dmitrymironov/usbpark/audi/images/bs.png

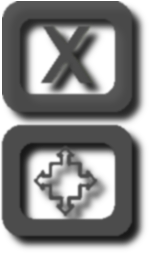
audi/images/bs.png
