dmitrymironov/usbpark/parktronic/images/PARKTRONIC_EMPTY.jpg

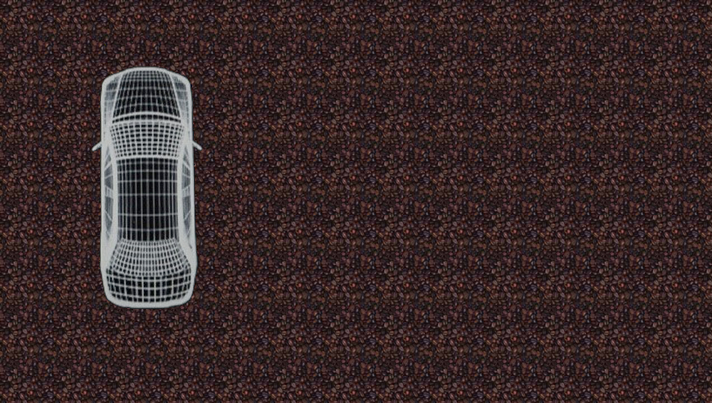
parktronic/images/PARKTRONIC_EMPTY.jpg
