dmitrymironov/usbpark/parktronic/images/PARKTRONIC_EMPTY_NO_VIDEO.jpg

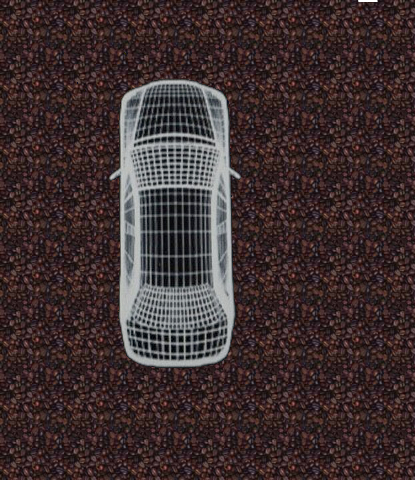
parktronic/images/PARKTRONIC_EMPTY_NO_VIDEO.jpg
