dmitrymironov/usbpark/parktronic/win32.cpp

/*
----------------------------------------------------------------------
CONTENTS of this file is private property of Novorado, LLC
======================================================================
Source Code is distributed for reference purposes only for Novorado 
customers. For other uses, please contact Novorado 
http://www.novorado.com or on our facebook/twitter page

You may use source code in your non-commercial and educational 
and customization projects free of charge.  

Novorado specializes in custom software and hardware design
and engineering services.
======================================================================
*/
#include	<list>
#include	<string>
#include	<deque>
#include	<iostream>

#ifndef _MSC_VER
#   include <wtypes.h>
#   include <unknwn.h>
#   include <ole2.h>
#   include <limits.h>
#   ifdef _WINGDI_
#      undef _WINGDI_
#   endif
#   define _WINGDI_ 1
#   define AM_NOVTABLE
#   define _OBJBASE_H_
#   undef _X86_
#   ifndef _I64_MAX
#     define _I64_MAX LONG_LONG_MAX
#   endif
#   define LONGLONG long long
#endif

#include	<dshow.h>

#include	"ParkSetup.h"

// Part of vlc_charset.h
#ifdef WIN32
//LIBVLC_USED
static inline char *FromWide (const wchar_t *wide)
{
    size_t len = WideCharToMultiByte (CP_UTF8, 0, wide, -1, NULL, 0, NULL, NULL);
    if (len == 0)
        return NULL;

    char *out = (char *)malloc (len);

    if (out)
        WideCharToMultiByte (CP_UTF8, 0, wide, -1, out, len, NULL, NULL);
    return out;
}
#endif

/* FindCaptureDevices:: This Function had two purposes :
    Returns the list of capture devices when p_listdevices != NULL
    Creates an IBaseFilter when p_devicename corresponds to an existing devname
   These actions *may* be requested whith a single call.
*/
#include	<ocidl.h>

static IBaseFilter *
FindCaptureDevice( std::string *p_devicename,
                   std::list<std::string> *p_listdevices, bool b_audio )
{
    IBaseFilter *p_base_filter = NULL;
    IMoniker *p_moniker = NULL;
    ULONG i_fetched;
    HRESULT hr;
    std::list<std::string> devicelist;

    /* Create the system device enumerator */
    ICreateDevEnum *p_dev_enum = NULL;

    hr = CoCreateInstance( CLSID_SystemDeviceEnum, NULL, CLSCTX_INPROC,
                           IID_ICreateDevEnum, (void **)&p_dev_enum );
    if( FAILED(hr) )
    {
        std::cerr << "failed to create the device enumerator (0x" << std::hex << hr << std::dec << ")" << std::endl;
        return NULL;
    }

    /* Create an enumerator for the video capture devices */
    IEnumMoniker *p_class_enum = NULL;
    if( !b_audio )
        hr = p_dev_enum->CreateClassEnumerator( CLSID_VideoInputDeviceCategory,
                                                &p_class_enum, 0 );
    else
        hr = p_dev_enum->CreateClassEnumerator( CLSID_AudioInputDeviceCategory,
                                                &p_class_enum, 0 );
    p_dev_enum->Release();
    if( FAILED(hr) )
    {
        std::cerr << "failed to create the class enumerator (0x" << std::hex << hr << std::dec << ")" << std::endl;
        return NULL;
    }

    /* If there are no enumerators for the requested type, then
     * CreateClassEnumerator will succeed, but p_class_enum will be NULL */
    if( p_class_enum == NULL )
    {
        std::cerr <<  "no " << ( b_audio ? "audio" : "video" ) << " capture device was detected" << std::endl;
        return NULL;
    }

    /* Enumerate the devices */

    /* Note that if the Next() call succeeds but there are no monikers,
     * it will return S_FALSE (which is not a failure). Therefore, we check
     * that the return code is S_OK instead of using SUCCEEDED() macro. */

    while( p_class_enum->Next( 1, &p_moniker, &i_fetched ) == S_OK )
    {
        /* Getting the property page to get the device name */
        IPropertyBag *p_bag;
        hr = p_moniker->BindToStorage( 0, 0, IID_IPropertyBag,
                                       (void **)&p_bag );
        if( SUCCEEDED(hr) )
        {
            VARIANT var;
            var.vt = VT_BSTR;
            hr = p_bag->Read( L"FriendlyName", &var, NULL );
            p_bag->Release();
            if( SUCCEEDED(hr) )
            {
                char *p_buf = FromWide( var.bstrVal );
                std::string devname = std::string(p_buf);
                free( p_buf) ;

                int dup = 0;
                /* find out if this name is already used by a previously found device */
                std::list<std::string>::const_iterator iter = devicelist.begin();
                std::list<std::string>::const_iterator end = devicelist.end();
                std::string ordevname = devname ;
                while ( iter != end )
                {
                    if( 0 == (*iter).compare( devname ) )
                    { /* devname is on the list. Try another name with sequence
                         number apended and then rescan until a unique entry is found*/
                         char seq[16];
                         snprintf(seq, 16, " #%d", ++dup);
                         devname = ordevname + seq;
                         iter = devicelist.begin();
                    }
                    else
                         ++iter;
                }
                devicelist.push_back( devname );

                if( p_devicename && *p_devicename == devname )
                {
                    std::cout << "asked for " << p_devicename->c_str() << ", binding to " << devname.c_str()  << std::endl;
                    /* NULL possibly means we don't need BindMoniker BindCtx ?? */
                    hr = p_moniker->BindToObject( NULL, 0, IID_IBaseFilter,
                                                  (void **)&p_base_filter );
                    if( FAILED(hr) )
                    {
                        std::cerr << "couldn't bind moniker to filter object (0x" << std::hex << hr << std::dec << ")" << std::endl;
                        p_moniker->Release();
                        p_class_enum->Release();
                        return NULL;
                    }
                    p_moniker->Release();
                    p_class_enum->Release();
                    return p_base_filter;
                }
            }
        }

        p_moniker->Release();
    }

    p_class_enum->Release();

    if( p_listdevices ) {
    devicelist.sort();
    *p_listdevices = devicelist;
    }
    return NULL;
}


std::list<std::string> Novorado::Parking::WebCamTab::getCaptureDevices()
{
	std::list<std::string> rv;
	bool b_audio=false;
	FindCaptureDevice(NULL,&rv,b_audio);
	return rv;
}
